Oshlo/ENCE461-Wacky-Racers-Assignment/src/mat91lib/sam4s/atmel/component/component_chipid.h

/**
 * \file
 *
 * Copyright (c) 2012 Atmel Corporation. All rights reserved.
 *
 * \asf_license_start
 *
 * \page License
 *
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
 * 3. The name of Atmel may not be used to endorse or promote products derived
 *    from this software without specific prior written permission.
 *
 * 4. This software may only be redistributed and used in connection with an
 *    Atmel microcontroller product.
 *
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
 * \asf_license_stop
 *
 */

#ifndef _SAM4S_CHIPID_COMPONENT_
#define _SAM4S_CHIPID_COMPONENT_

/* ============================================================================= */
/**  SOFTWARE API DEFINITION FOR Chip Identifier */
/* ============================================================================= */
/** \addtogroup SAM4S_CHIPID Chip Identifier */
/*@{*/

#if !(defined(__ASSEMBLY__) || defined(__IAR_SYSTEMS_ASM__))
/** \brief Chipid hardware registers */
typedef struct {
  RoReg CHIPID_CIDR; /**< \brief (Chipid Offset: 0x0) Chip ID Register */
  RoReg CHIPID_EXID; /**< \brief (Chipid Offset: 0x4) Chip ID Extension Register */
} Chipid;
#endif /* !(defined(__ASSEMBLY__) || defined(__IAR_SYSTEMS_ASM__)) */
/* -------- CHIPID_CIDR : (CHIPID Offset: 0x0) Chip ID Register -------- */
#define CHIPID_CIDR_VERSION_Pos 0
#define CHIPID_CIDR_VERSION_Msk (0x1fu << CHIPID_CIDR_VERSION_Pos) /**< \brief (CHIPID_CIDR) Version of the Device */
#define CHIPID_CIDR_EPROC_Pos 5
#define CHIPID_CIDR_EPROC_Msk (0x7u << CHIPID_CIDR_EPROC_Pos) /**< \brief (CHIPID_CIDR) Embedded Processor */
#define   CHIPID_CIDR_EPROC_ARM946ES (0x1u << 5) /**< \brief (CHIPID_CIDR) ARM946ES */
#define   CHIPID_CIDR_EPROC_ARM7TDMI (0x2u << 5) /**< \brief (CHIPID_CIDR) ARM7TDMI */
#define   CHIPID_CIDR_EPROC_CM3 (0x3u << 5) /**< \brief (CHIPID_CIDR) Cortex-M3 */
#define   CHIPID_CIDR_EPROC_ARM920T (0x4u << 5) /**< \brief (CHIPID_CIDR) ARM920T */
#define   CHIPID_CIDR_EPROC_ARM926EJS (0x5u << 5) /**< \brief (CHIPID_CIDR) ARM926EJS */
#define   CHIPID_CIDR_EPROC_CA5 (0x6u << 5) /**< \brief (CHIPID_CIDR) Cortex-A5 */
#define   CHIPID_CIDR_EPROC_CM4 (0x7u << 5) /**< \brief (CHIPID_CIDR) Cortex-M4 */
#define CHIPID_CIDR_NVPSIZ_Pos 8
#define CHIPID_CIDR_NVPSIZ_Msk (0xfu << CHIPID_CIDR_NVPSIZ_Pos) /**< \brief (CHIPID_CIDR) Nonvolatile Program Memory Size */
#define   CHIPID_CIDR_NVPSIZ_NONE (0x0u << 8) /**< \brief (CHIPID_CIDR) None */
#define   CHIPID_CIDR_NVPSIZ_8K (0x1u << 8) /**< \brief (CHIPID_CIDR) 8K bytes */
#define   CHIPID_CIDR_NVPSIZ_16K (0x2u << 8) /**< \brief (CHIPID_CIDR) 16K bytes */
#define   CHIPID_CIDR_NVPSIZ_32K (0x3u << 8) /**< \brief (CHIPID_CIDR) 32K bytes */
#define   CHIPID_CIDR_NVPSIZ_64K (0x5u << 8) /**< \brief (CHIPID_CIDR) 64K bytes */
#define   CHIPID_CIDR_NVPSIZ_128K (0x7u << 8) /**< \brief (CHIPID_CIDR) 128K bytes */
#define   CHIPID_CIDR_NVPSIZ_256K (0x9u << 8) /**< \brief (CHIPID_CIDR) 256K bytes */
#define   CHIPID_CIDR_NVPSIZ_512K (0xAu << 8) /**< \brief (CHIPID_CIDR) 512K bytes */
#define   CHIPID_CIDR_NVPSIZ_1024K (0xCu << 8) /**< \brief (CHIPID_CIDR) 1024K bytes */
#define   CHIPID_CIDR_NVPSIZ_2048K (0xEu << 8) /**< \brief (CHIPID_CIDR) 2048K bytes */
#define CHIPID_CIDR_NVPSIZ2_Pos 12
#define CHIPID_CIDR_NVPSIZ2_Msk (0xfu << CHIPID_CIDR_NVPSIZ2_Pos) /**< \brief (CHIPID_CIDR)  */
#define   CHIPID_CIDR_NVPSIZ2_NONE (0x0u << 12) /**< \brief (CHIPID_CIDR) None */
#define   CHIPID_CIDR_NVPSIZ2_8K (0x1u << 12) /**< \brief (CHIPID_CIDR) 8K bytes */
#define   CHIPID_CIDR_NVPSIZ2_16K (0x2u << 12) /**< \brief (CHIPID_CIDR) 16K bytes */
#define   CHIPID_CIDR_NVPSIZ2_32K (0x3u << 12) /**< \brief (CHIPID_CIDR) 32K bytes */
#define   CHIPID_CIDR_NVPSIZ2_64K (0x5u << 12) /**< \brief (CHIPID_CIDR) 64K bytes */
#define   CHIPID_CIDR_NVPSIZ2_128K (0x7u << 12) /**< \brief (CHIPID_CIDR) 128K bytes */
#define   CHIPID_CIDR_NVPSIZ2_256K (0x9u << 12) /**< \brief (CHIPID_CIDR) 256K bytes */
#define   CHIPID_CIDR_NVPSIZ2_512K (0xAu << 12) /**< \brief (CHIPID_CIDR) 512K bytes */
#define   CHIPID_CIDR_NVPSIZ2_1024K (0xCu << 12) /**< \brief (CHIPID_CIDR) 1024K bytes */
#define   CHIPID_CIDR_NVPSIZ2_2048K (0xEu << 12) /**< \brief (CHIPID_CIDR) 2048K bytes */
#define CHIPID_CIDR_SRAMSIZ_Pos 16
#define CHIPID_CIDR_SRAMSIZ_Msk (0xfu << CHIPID_CIDR_SRAMSIZ_Pos) /**< \brief (CHIPID_CIDR) Internal SRAM Size */
#define   CHIPID_CIDR_SRAMSIZ_48K (0x0u << 16) /**< \brief (CHIPID_CIDR) 48K bytes */
#define   CHIPID_CIDR_SRAMSIZ_1K (0x1u << 16) /**< \brief (CHIPID_CIDR) 1K bytes */
#define   CHIPID_CIDR_SRAMSIZ_2K (0x2u << 16) /**< \brief (CHIPID_CIDR) 2K bytes */
#define   CHIPID_CIDR_SRAMSIZ_6K (0x3u << 16) /**< \brief (CHIPID_CIDR) 6K bytes */
#define   CHIPID_CIDR_SRAMSIZ_24K (0x4u << 16) /**< \brief (CHIPID_CIDR) 24K bytes */
#define   CHIPID_CIDR_SRAMSIZ_4K (0x5u << 16) /**< \brief (CHIPID_CIDR) 4K bytes */
#define   CHIPID_CIDR_SRAMSIZ_80K (0x6u << 16) /**< \brief (CHIPID_CIDR) 80K bytes */
#define   CHIPID_CIDR_SRAMSIZ_160K (0x7u << 16) /**< \brief (CHIPID_CIDR) 160K bytes */
#define   CHIPID_CIDR_SRAMSIZ_8K (0x8u << 16) /**< \brief (CHIPID_CIDR) 8K bytes */
#define   CHIPID_CIDR_SRAMSIZ_16K (0x9u << 16) /**< \brief (CHIPID_CIDR) 16K bytes */
#define   CHIPID_CIDR_SRAMSIZ_32K (0xAu << 16) /**< \brief (CHIPID_CIDR) 32K bytes */
#define   CHIPID_CIDR_SRAMSIZ_64K (0xBu << 16) /**< \brief (CHIPID_CIDR) 64K bytes */
#define   CHIPID_CIDR_SRAMSIZ_128K (0xCu << 16) /**< \brief (CHIPID_CIDR) 128K bytes */
#define   CHIPID_CIDR_SRAMSIZ_256K (0xDu << 16) /**< \brief (CHIPID_CIDR) 256K bytes */
#define   CHIPID_CIDR_SRAMSIZ_96K (0xEu << 16) /**< \brief (CHIPID_CIDR) 96K bytes */
#define   CHIPID_CIDR_SRAMSIZ_512K (0xFu << 16) /**< \brief (CHIPID_CIDR) 512K bytes */
#define CHIPID_CIDR_ARCH_Pos 20
#define CHIPID_CIDR_ARCH_Msk (0xffu << CHIPID_CIDR_ARCH_Pos) /**< \brief (CHIPID_CIDR) Architecture Identifier */
#define   CHIPID_CIDR_ARCH_AT91SAM9xx (0x19u << 20) /**< \brief (CHIPID_CIDR) AT91SAM9xx Series */
#define   CHIPID_CIDR_ARCH_AT91SAM9XExx (0x29u << 20) /**< \brief (CHIPID_CIDR) AT91SAM9XExx Series */
#define   CHIPID_CIDR_ARCH_AT91x34 (0x34u << 20) /**< \brief (CHIPID_CIDR) AT91x34 Series */
#define   CHIPID_CIDR_ARCH_CAP7 (0x37u << 20) /**< \brief (CHIPID_CIDR) CAP7 Series */
#define   CHIPID_CIDR_ARCH_CAP9 (0x39u << 20) /**< \brief (CHIPID_CIDR) CAP9 Series */
#define   CHIPID_CIDR_ARCH_CAP11 (0x3Bu << 20) /**< \brief (CHIPID_CIDR) CAP11 Series */
#define   CHIPID_CIDR_ARCH_AT91x40 (0x40u << 20) /**< \brief (CHIPID_CIDR) AT91x40 Series */
#define   CHIPID_CIDR_ARCH_AT91x42 (0x42u << 20) /**< \brief (CHIPID_CIDR) AT91x42 Series */
#define   CHIPID_CIDR_ARCH_AT91x55 (0x55u << 20) /**< \brief (CHIPID_CIDR) AT91x55 Series */
#define   CHIPID_CIDR_ARCH_AT91SAM7Axx (0x60u << 20) /**< \brief (CHIPID_CIDR) AT91SAM7Axx Series */
#define   CHIPID_CIDR_ARCH_AT91SAM7AQxx (0x61u << 20) /**< \brief (CHIPID_CIDR) AT91SAM7AQxx Series */
#define   CHIPID_CIDR_ARCH_AT91x63 (0x63u << 20) /**< \brief (CHIPID_CIDR) AT91x63 Series */
#define   CHIPID_CIDR_ARCH_AT91SAM7Sxx (0x70u << 20) /**< \brief (CHIPID_CIDR) AT91SAM7Sxx Series */
#define   CHIPID_CIDR_ARCH_AT91SAM7XCxx (0x71u << 20) /**< \brief (CHIPID_CIDR) AT91SAM7XCxx Series */
#define   CHIPID_CIDR_ARCH_AT91SAM7SExx (0x72u << 20) /**< \brief (CHIPID_CIDR) AT91SAM7SExx Series */
#define   CHIPID_CIDR_ARCH_AT91SAM7Lxx (0x73u << 20) /**< \brief (CHIPID_CIDR) AT91SAM7Lxx Series */
#define   CHIPID_CIDR_ARCH_AT91SAM7Xxx (0x75u << 20) /**< \brief (CHIPID_CIDR) AT91SAM7Xxx Series */
#define   CHIPID_CIDR_ARCH_AT91SAM7SLxx (0x76u << 20) /**< \brief (CHIPID_CIDR) AT91SAM7SLxx Series */
#define   CHIPID_CIDR_ARCH_SAM3UxC (0x80u << 20) /**< \brief (CHIPID_CIDR) SAM3UxC Series (100-pin version) */
#define   CHIPID_CIDR_ARCH_SAM3UxE (0x81u << 20) /**< \brief (CHIPID_CIDR) SAM3UxE Series (144-pin version) */
#define   CHIPID_CIDR_ARCH_SAM3ASAM4AxC (0x83u << 20) /**< \brief (CHIPID_CIDR) SAM3AxC or SAM4AxC Series (100-pin version) */
#define   CHIPID_CIDR_ARCH_SAM3XSAM4XxC (0x84u << 20) /**< \brief (CHIPID_CIDR) SAM3XxCor SAM4XxC Series (100-pin version) */
#define   CHIPID_CIDR_ARCH_SAM3XSAM4XxE (0x85u << 20) /**< \brief (CHIPID_CIDR) SAM3XxEor SAM4XxE Series (144-pin version) */
#define   CHIPID_CIDR_ARCH_SAM3XSAM4XxG (0x86u << 20) /**< \brief (CHIPID_CIDR) SAM3XxGor or SAM4XxG Series  (208/217-pin version) */
#define   CHIPID_CIDR_ARCH_SAM3SSAM4SxA (0x88u << 20) /**< \brief (CHIPID_CIDR) SAM3SxA or SAM4SxA Series (48-pin version) */
#define   CHIPID_CIDR_ARCH_SAM3SSAM4SxB (0x89u << 20) /**< \brief (CHIPID_CIDR) SAM3SxBor SAM4SxB Series (64-pin version) */
#define   CHIPID_CIDR_ARCH_SAM3SSAM4SxC (0x8Au << 20) /**< \brief (CHIPID_CIDR) SAM3SxCor SAM4SxC Series (100-pin version) */
#define   CHIPID_CIDR_ARCH_AT91x92 (0x92u << 20) /**< \brief (CHIPID_CIDR) AT91x92 Series */
#define   CHIPID_CIDR_ARCH_SAM3NxA (0x93u << 20) /**< \brief (CHIPID_CIDR) SAM3NxA Series (48-pin version) */
#define   CHIPID_CIDR_ARCH_SAM3NxB (0x94u << 20) /**< \brief (CHIPID_CIDR) SAM3NxB Series (64-pin version) */
#define   CHIPID_CIDR_ARCH_SAM3NxC (0x95u << 20) /**< \brief (CHIPID_CIDR) SAM3NxC Series (100-pin version) */
#define   CHIPID_CIDR_ARCH_SAM3SDxB (0x99u << 20) /**< \brief (CHIPID_CIDR) SAM3SDxB Series (64-pin version) */
#define   CHIPID_CIDR_ARCH_SAM3SDxC (0x9Au << 20) /**< \brief (CHIPID_CIDR) SAM3SDxC Series (100-pin version) */
#define   CHIPID_CIDR_ARCH_SAM5A (0xA5u << 20) /**< \brief (CHIPID_CIDR) SAM5A */
#define   CHIPID_CIDR_ARCH_AT75Cxx (0xF0u << 20) /**< \brief (CHIPID_CIDR) AT75Cxx Series */
#define CHIPID_CIDR_NVPTYP_Pos 28
#define CHIPID_CIDR_NVPTYP_Msk (0x7u << CHIPID_CIDR_NVPTYP_Pos) /**< \brief (CHIPID_CIDR) Nonvolatile Program Memory Type */
#define   CHIPID_CIDR_NVPTYP_ROM (0x0u << 28) /**< \brief (CHIPID_CIDR) ROM */
#define   CHIPID_CIDR_NVPTYP_ROMLESS (0x1u << 28) /**< \brief (CHIPID_CIDR) ROMless or on-chip Flash */
#define   CHIPID_CIDR_NVPTYP_FLASH (0x2u << 28) /**< \brief (CHIPID_CIDR) Embedded Flash Memory */
#define   CHIPID_CIDR_NVPTYP_ROM_FLASH (0x3u << 28) /**< \brief (CHIPID_CIDR) ROM and Embedded Flash MemoryNVPSIZ is ROM size      NVPSIZ2 is Flash size */
#define   CHIPID_CIDR_NVPTYP_SRAM (0x4u << 28) /**< \brief (CHIPID_CIDR) SRAM emulating ROM */
#define CHIPID_CIDR_EXT (0x1u << 31) /**< \brief (CHIPID_CIDR) Extension Flag */
/* -------- CHIPID_EXID : (CHIPID Offset: 0x4) Chip ID Extension Register -------- */
#define CHIPID_EXID_EXID_Pos 0
#define CHIPID_EXID_EXID_Msk (0xffffffffu << CHIPID_EXID_EXID_Pos) /**< \brief (CHIPID_EXID) Chip ID Extension */

/*@}*/


#endif /* _SAM4S_CHIPID_COMPONENT_ */
