Oshlo/ENCE461-Wacky-Racers-Assignment/src/mat91lib/cadc/cadc.c

/** @file   cadc.c
    @author M. P. Hayes
    @date   12 February 2020
    @brief  Continuuous analogue to digital converter using DMA
*/


#include <stdlib.h>
#include <string.h>
#include "cadc.h"
#include "adc.h"
#include "pdc.h"
#include "irq.h"
#include "delay.h"


#ifndef ADC_IRQ_PRIORITY
#define ADC_IRQ_PRIORITY 4
#endif    


struct cadc_dev
{
    tc_t tc;
    pdc_t pdc;
    adc_t adc;
    uint16_t dma_size;
    uint16_t *prev;
    uint32_t count;
    uint8_t num_channels;
    volatile uint32_t isr_count;
    uint8_t num_buffers;
    bool started;
    pdc_descriptor_t *descriptors;
    volatile adc_sample_t **buffers;
    void *callback_data;
    cadc_callback_t callback_func;
};


static struct cadc_dev cadc_dev;



static void
cadc_isr (void)
{
    pdc_descriptor_t *descr;
    cadc_t dev = &cadc_dev;
    
    descr = pdc_read_poll (dev->pdc);

    // Something is wrong if the descriptor is zero; it means the
    // transfer has not finished.  Perhaps another ADC interrupt is
    // enabled?
    if (!descr)
        return;

    dev->isr_count++;

    if (dev->callback_func)
        dev->callback_func (dev->callback_data, descr->buffer,
                            dev->prev, dev->dma_size);
    
    dev->prev = descr->buffer;
}


cadc_t cadc_init (const cadc_cfg_t *cfg)
{
    int i;
    uint32_t channels;
    uint8_t num_channels;
    cadc_t dev = &cadc_dev;

    dev->callback_func = 0;
    
    dev->dma_size = cfg->dma_size;
    dev->num_buffers = cfg->num_buffers;
    if (dev->num_buffers < 3)
        dev->num_buffers = 3;

    /* Generate sampling clock.  */
    dev->tc = tc_init (&cfg->tc);
    if (! dev->tc)
        return 0;

    dev->adc = adc_init (&cfg->adc);
    if (! dev->adc)
        return 0;

    tc_start (dev->tc);

    channels = cfg->adc.channels;
    num_channels = 0;
    while (channels)
    {
        if (channels & 1)
            num_channels++;
        channels >>= 1;
    }
    dev->num_channels = num_channels;

    if (! num_channels)
        return 0;

    dev->descriptors = calloc (dev->num_buffers, sizeof (*dev->descriptors));
    
    for (i = 0; i < dev->num_buffers; i++)
    {
        dev->descriptors[i].buffer = calloc (dev->dma_size, sizeof (uint16_t));
        dev->descriptors[i].size = dev->dma_size;
        dev->descriptors[i].next = &dev->descriptors[(i + 1) % dev->num_buffers];
    }

    dev->prev = 0;
    dev->started = 0;
    dev->pdc = pdc_init (adc_pdc_get (dev->adc), 0, dev->descriptors);

    ADC->ADC_IER = ADC_ISR_ENDRX;
    irq_config (ID_ADC, ADC_IRQ_PRIORITY, cadc_isr);
    irq_enable (ID_ADC);
    
    return dev;
}


void
cadc_start (cadc_t dev)
{
    if (dev->started)
        return;
    
    pdc_config (dev->pdc, 0, dev->descriptors);

    // There is a problem with restarting.   It sees like the ADC
    // needs a hardware reset to reset the multiplexer sequencer
    // but something is not configured correctly after the reset.
    // It is best to leave the ADC running.
    
    adc_enable (dev->adc);
    pdc_start (dev->pdc);
    dev->count = 0;
    dev->prev = 0;
    dev->started = 1;
    dev->prev = 0;    
}


void
cadc_stop (cadc_t dev)
{
    // adc_disable does nothing; the ADC runs on...
    adc_disable (dev->adc);
    // ... but the DMA is stopped
    pdc_stop (dev->pdc);
}


void
cadc_shutdown (cadc_t dev)
{
    cadc_stop (dev);
    adc_shutdown (dev->adc);
    tc_shutdown (dev->tc);
}


void cadc_callback_register (cadc_t dev,
                             cadc_callback_t callback_func,
                             void *callback_data)
{
    dev->callback_func = callback_func;
    dev->callback_data = callback_data;    
}


uint8_t cadc_num_channels_get (cadc_t dev)
{
    return dev->num_channels;
}
